jordankooyman/Diacritic_Keypad/diacritc keypad finished perspective view.jpg

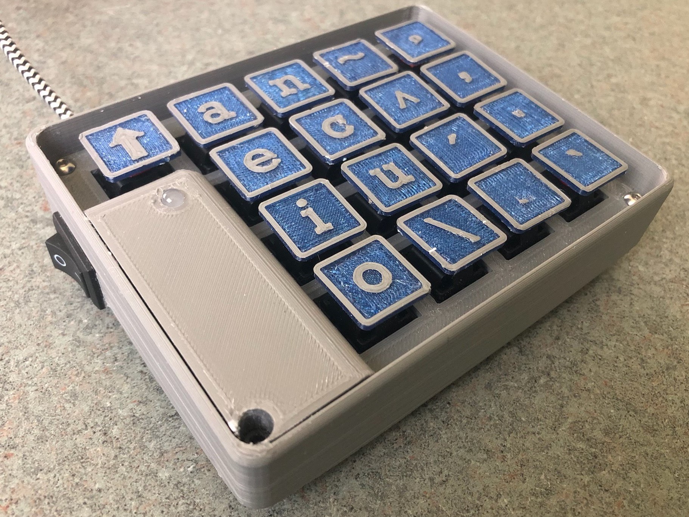
diacritc keypad finished perspective view.jpg
