jordankooyman/Diacritic_Keypad/diacritc keypad finished top view.jpg

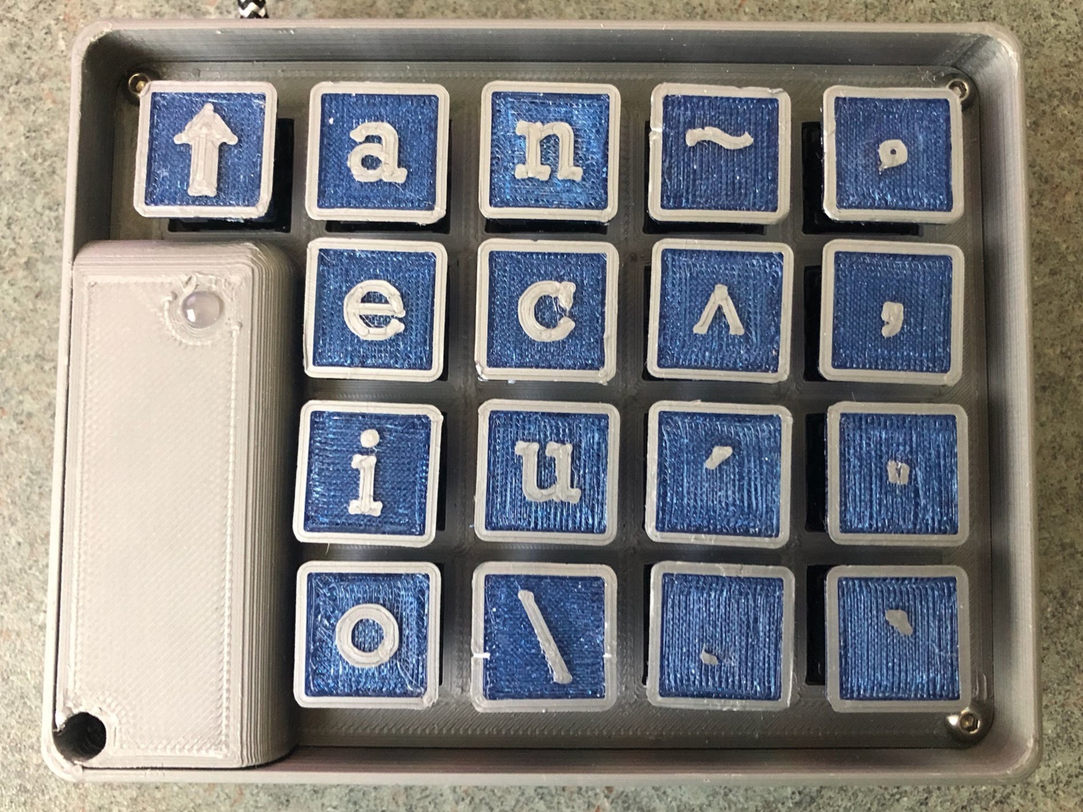
diacritc keypad finished top view.jpg
