jordankooyman/Diacritic_Keypad/Example Wiring Photos/Arduino Wiring (4).JPG

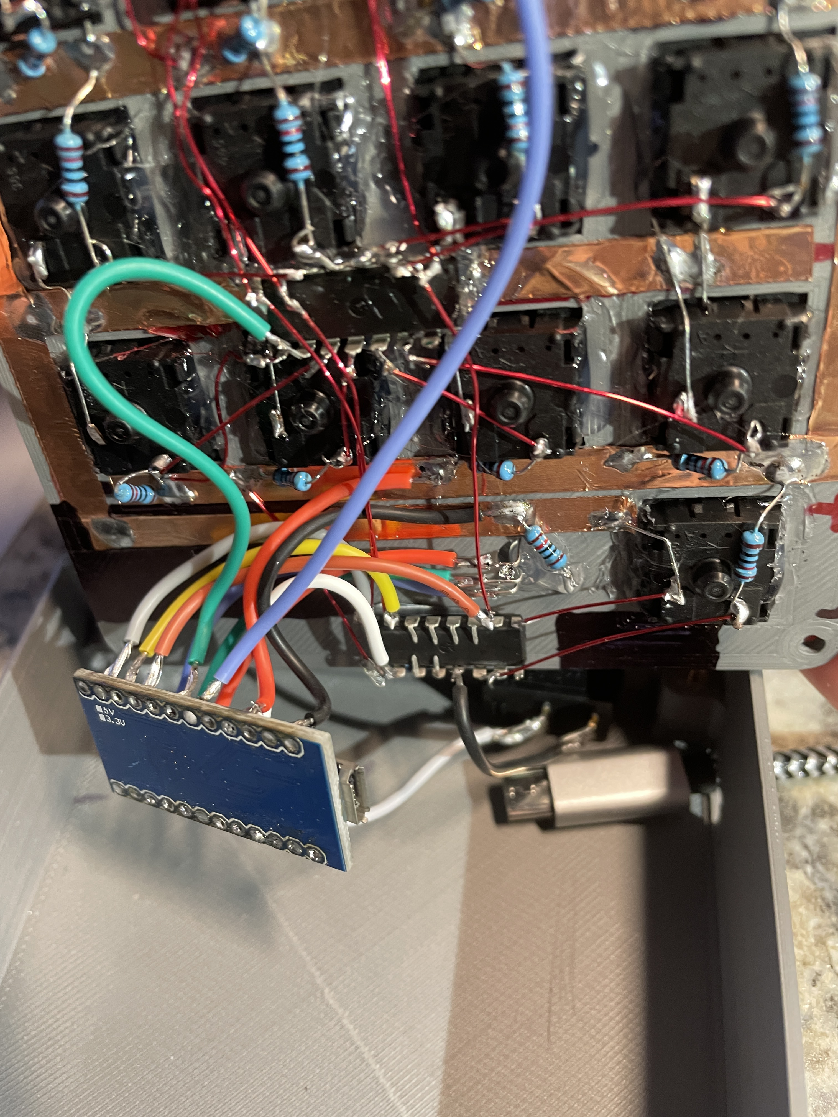
Example Wiring Photos/Arduino Wiring (4).JPG
