jordankooyman/Diacritic_Keypad/Example Wiring Photos/Full Wiring with Capacitors (5).JPG

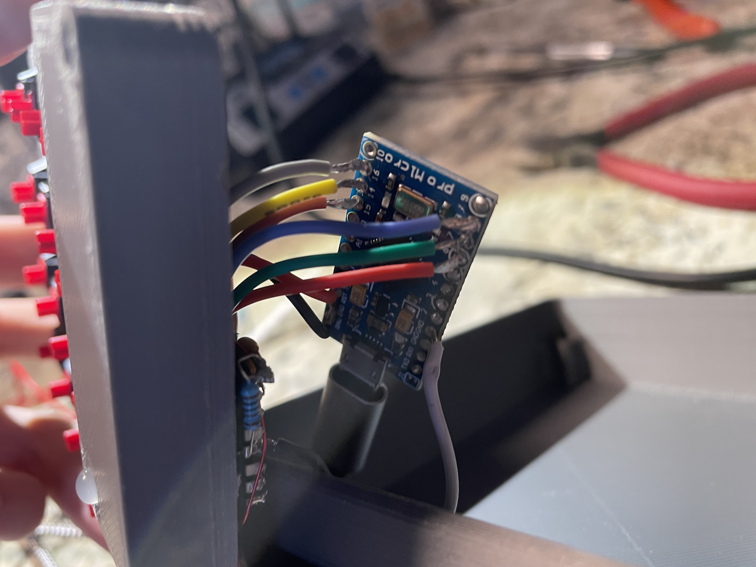
Example Wiring Photos/Full Wiring with Capacitors (5).JPG
