jordankooyman/Diacritic_Keypad/Example Wiring Photos/Full Wiring with Capacitors (6).JPG

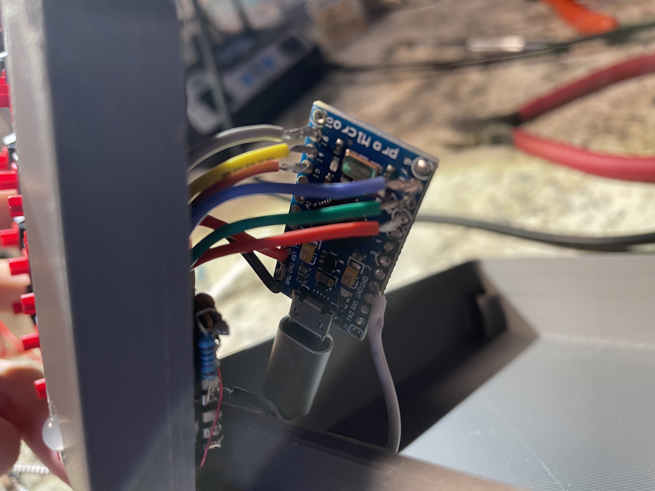
Example Wiring Photos/Full Wiring with Capacitors (6).JPG
