jordankooyman/Diacritic_Keypad/Example Wiring Photos/Full Wiring with Capacitors (7).JPG

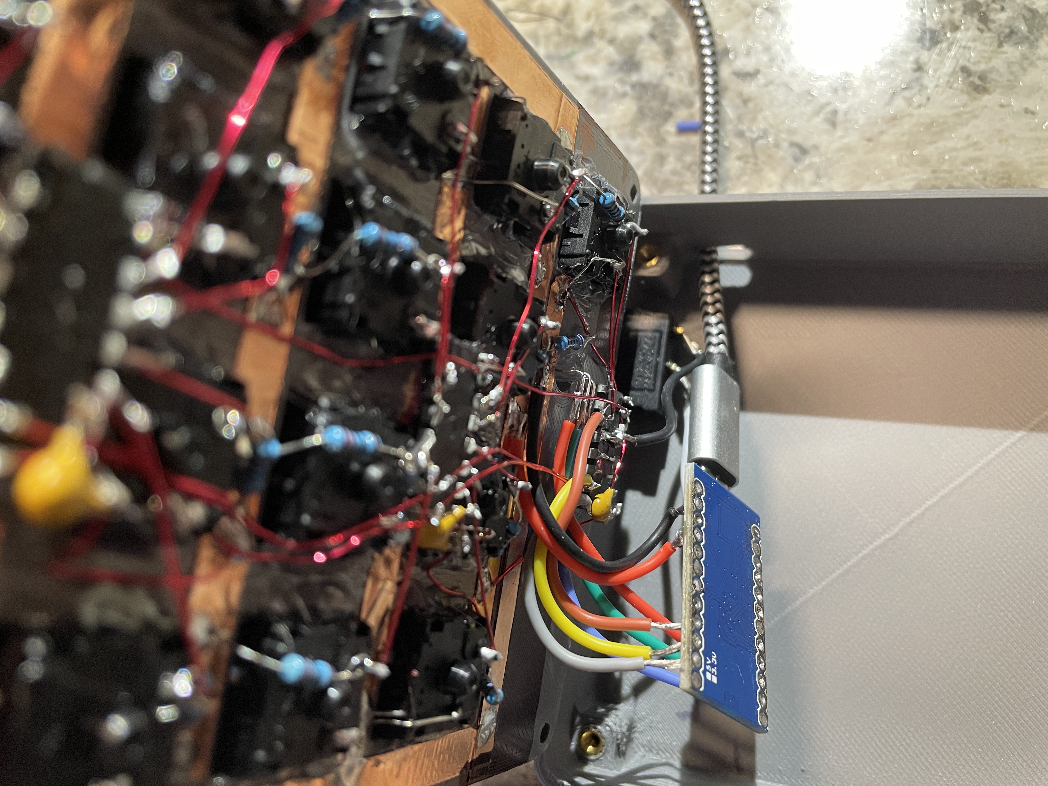
Example Wiring Photos/Full Wiring with Capacitors (7).JPG
