jordankooyman/Diacritic_Keypad/Example Wiring Photos/Arduino Wiring (6).JPG

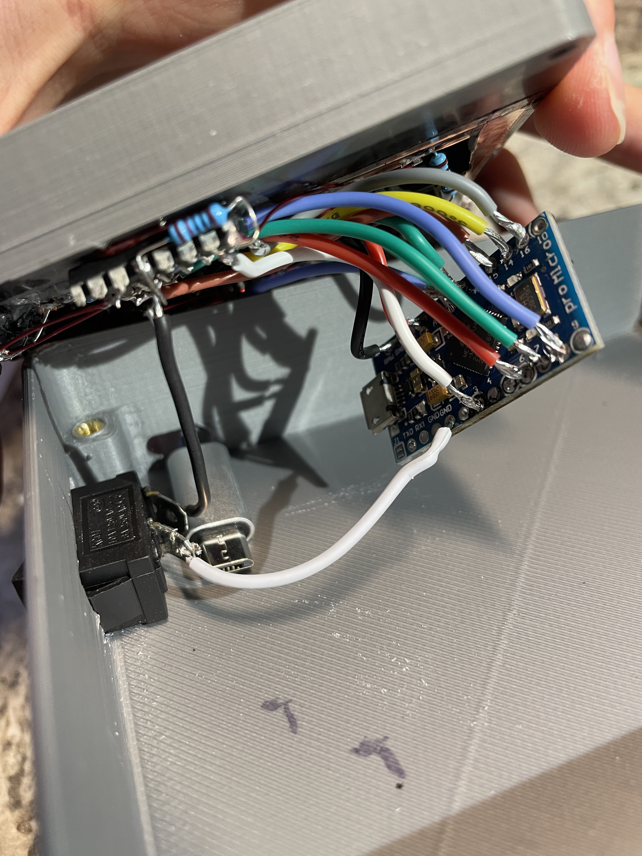
Example Wiring Photos/Arduino Wiring (6).JPG
