jordankooyman/Diacritic_Keypad/Example Wiring Photos/Arduino Wiring (7).JPG

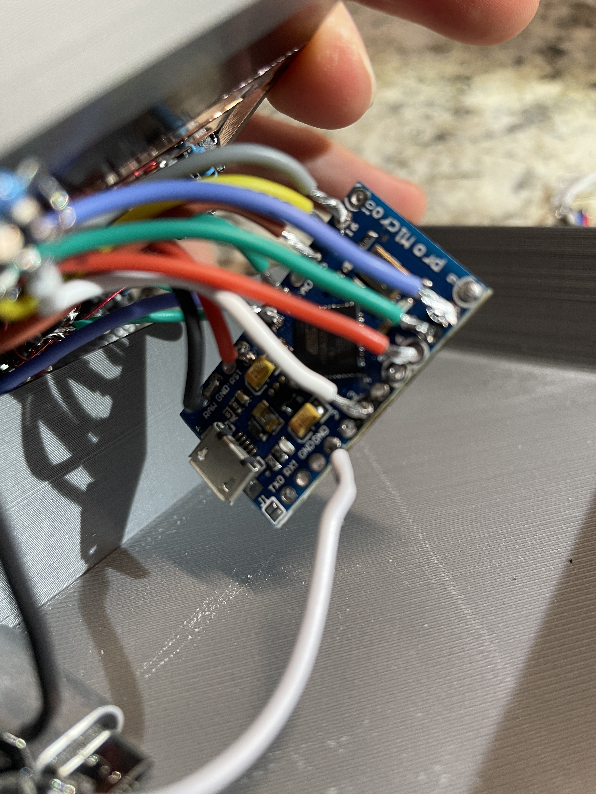
Example Wiring Photos/Arduino Wiring (7).JPG
