jordankooyman/Diacritic_Keypad/Example Wiring Photos/Arduino Wiring (9).JPG

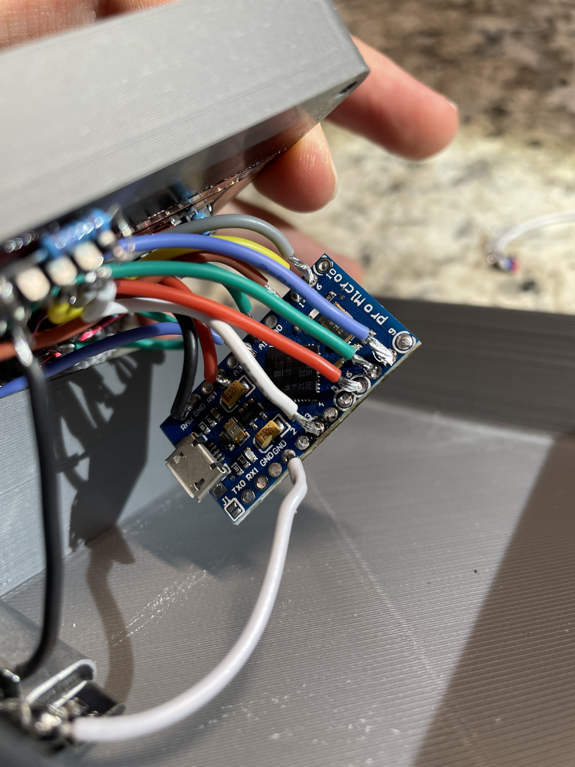
Example Wiring Photos/Arduino Wiring (9).JPG
