jordankooyman/Diacritic_Keypad/Example Wiring Photos/Final Product (1).JPG

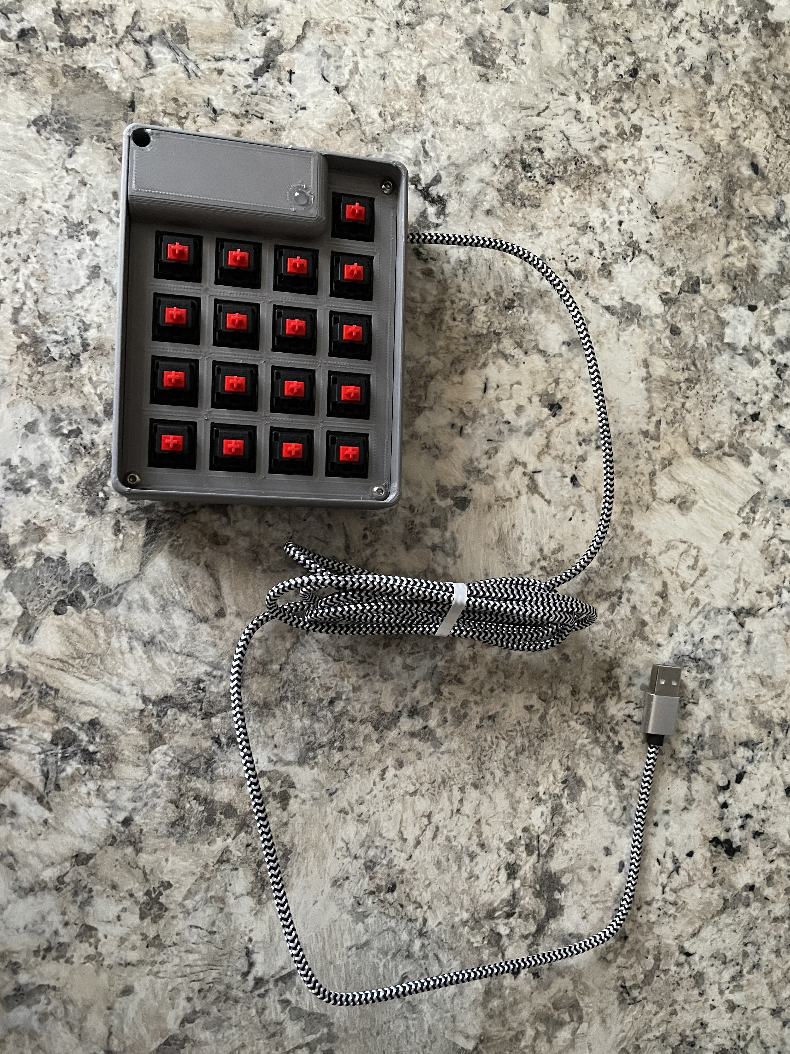
Example Wiring Photos/Final Product (1).JPG
