jordankooyman/Diacritic_Keypad/Example Wiring Photos/Full Wiring with Capacitors (3).JPG

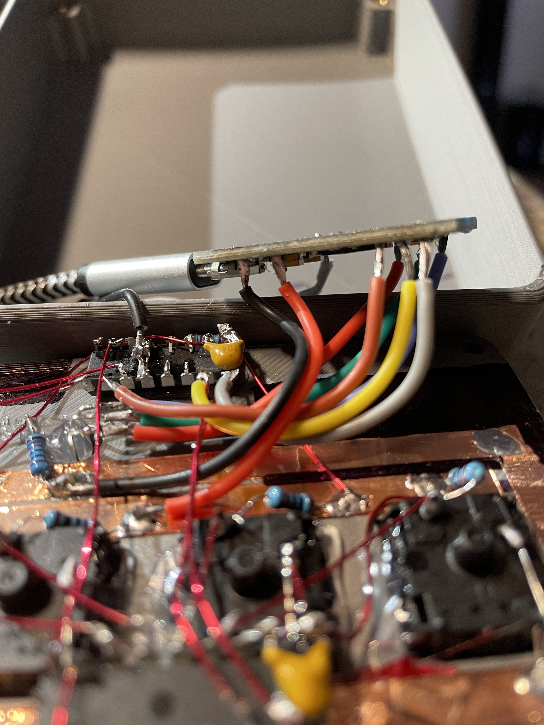
Example Wiring Photos/Full Wiring with Capacitors (3).JPG
